Parzival4o4/another_deej_controller/Assets/Pictures/1.jpg

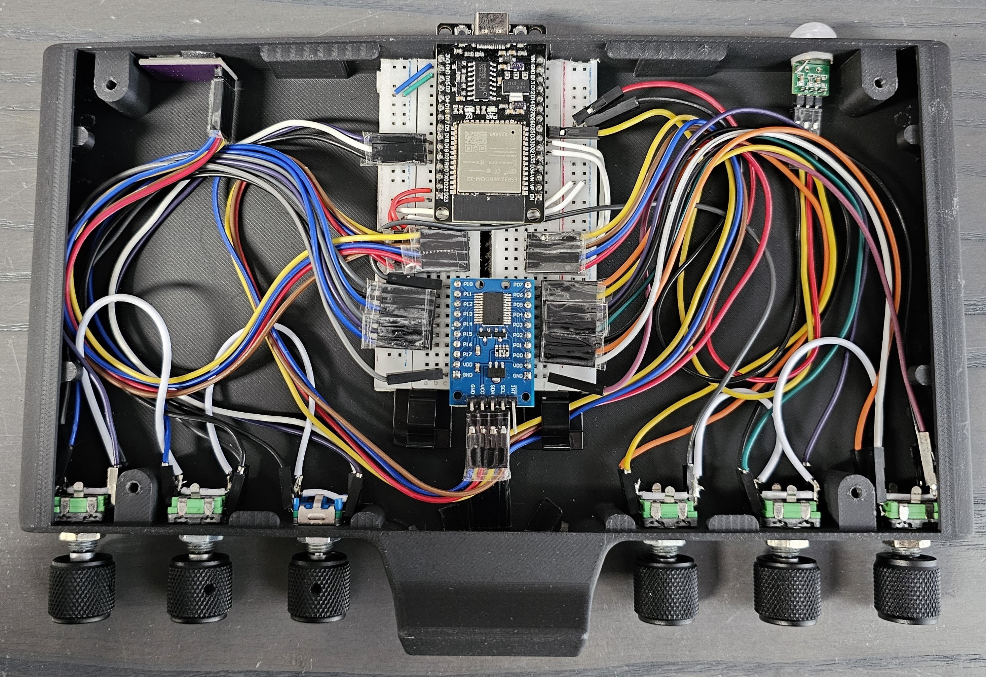
Assets/Pictures/1.jpg
