Parzival4o4/another_deej_controller/Assets/Pictures/2.jpg

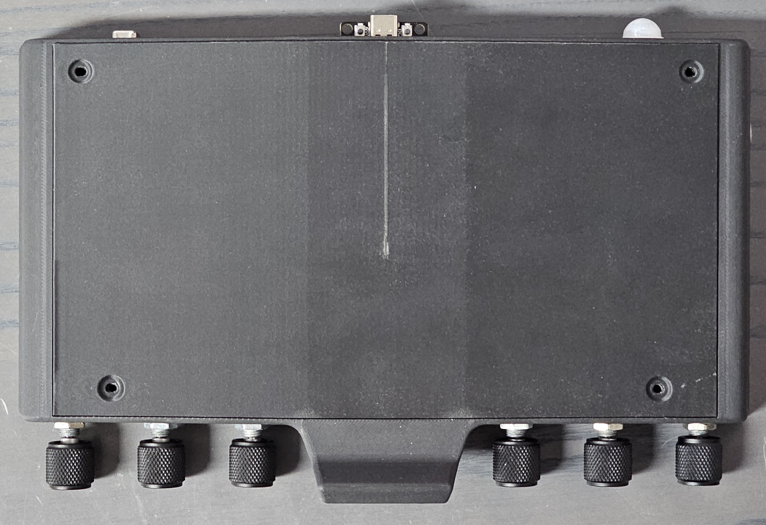
Assets/Pictures/2.jpg
