Parzival4o4/another_deej_controller/arduino-project/controller_firmware/CAB_Input_device.ino

// abstract class, represents a input device
//#################################################################
class Input_device {
  //###############################################################
public:
  virtual ~Input_device() {}

  virtual bool add_input(std::vector<std::unique_ptr<StateChange>>& vec);
  // return true if you added something
};
